mustang51/toro-ufc/fw/src/analog.cpp

#include <Arduino.h>

#include "analog.h"
#include "misc.h"
#include "joystick.h"

static const unsigned int ANALOG_POLL_MS = 20;

static const unsigned long EMA_MAX   = 128;
static const unsigned long EMA_ALPHA = 32;

static const uint8_t channels[] = {2, 1, 0, 3, 4, 5};
static const bool channels_invert[] = {false, false, true, true, false, false};
static const unsigned int analogs = sizeof(channels);
static const uint8_t buttons[][2] = {
	{69, 70},
	{71, 72},
	{73, 74},
	{75, 76},
	{77, 78},
	{79, 80}
};

static unsigned long EMA_LP[] = {0, 0, 0, 0, 0, 0};
static unsigned int values[] = {300, 300, 300, 300, 300, 300};

void ema_low_pass_filter(unsigned int index, unsigned long new_value)
{
	EMA_LP[index] = (EMA_ALPHA * new_value +
			 (EMA_MAX - EMA_ALPHA) * EMA_LP[index]) / EMA_MAX;
}

bool low_pass(unsigned int index)
{
	unsigned int current = values[index] * 16;
	unsigned int ema = EMA_LP[index];

	if (abs(ema - current) < 32)
		return false;

	values[index] = ema / 16;

	return true;
}

void analog_loop(void)
{
	static unsigned long next_millis = 0;
	if (! time_expired_from(millis(), next_millis))
		return;
	next_millis += ANALOG_POLL_MS;

	for (unsigned int a = 0; a < analogs; a++) {
		unsigned int reading = analogRead(channels[a]);
		if (channels_invert[a])
			reading = 4095 - reading;
		ema_low_pass_filter(a, reading);
		if (low_pass(a)) {
			Joystick.setAxis(a, values[a]);
			if (values[a] <= 5) {
				Joystick.setButton(buttons[a][1], false);
				Joystick.setButton(buttons[a][0], true);
			} else if (values[a] >= 250) {
				Joystick.setButton(buttons[a][0], false);
				Joystick.setButton(buttons[a][1], true);
			} else {
				Joystick.setButton(buttons[a][0], false);
				Joystick.setButton(buttons[a][1], false);
			}
		}
	}

	return;
}

void analog_setup(void)
{

}
